FLRHW/Strobe_HMI/HTML/images/cat_pdf_drill_map_Strobe_HMI-PTH_drill_map.png

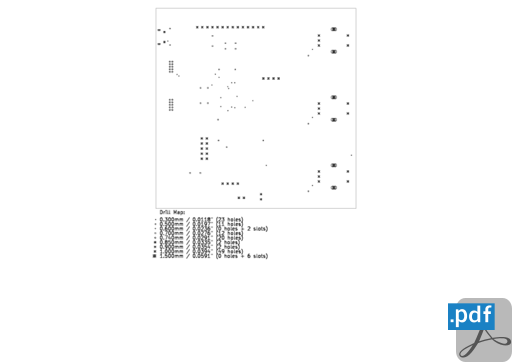
HTML/images/cat_pdf_drill_map_Strobe_HMI-PTH_drill_map.png
