FLRHW/Strobe_HMI/HTML/images/cat_png_3d_viewer_angled_bottom_Strobe_HMI-angled_bottom.png

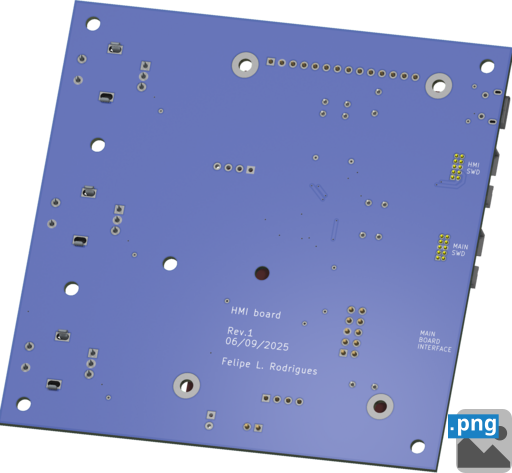
HTML/images/cat_png_3d_viewer_angled_bottom_Strobe_HMI-angled_bottom.png
