FLRHW/Strobe_HMI/HTML/images/cat_png_3d_viewer_angled_top_Strobe_HMI-angled_top.png

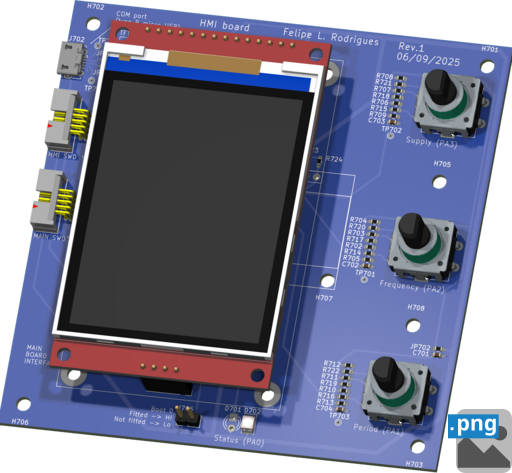
HTML/images/cat_png_3d_viewer_angled_top_Strobe_HMI-angled_top.png
