FLRHW/Strobe_HMI/HTML/images/cat_png_3d_viewer_top_Strobe_HMI-top.png

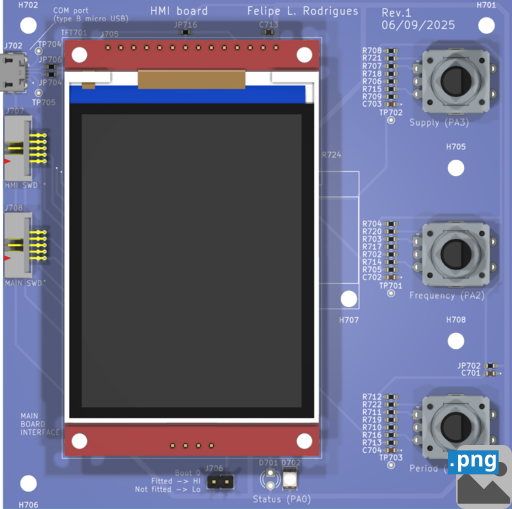
HTML/images/cat_png_3d_viewer_top_Strobe_HMI-top.png
