FLRHW/Strobe_HMI/Images/BOT.jpg

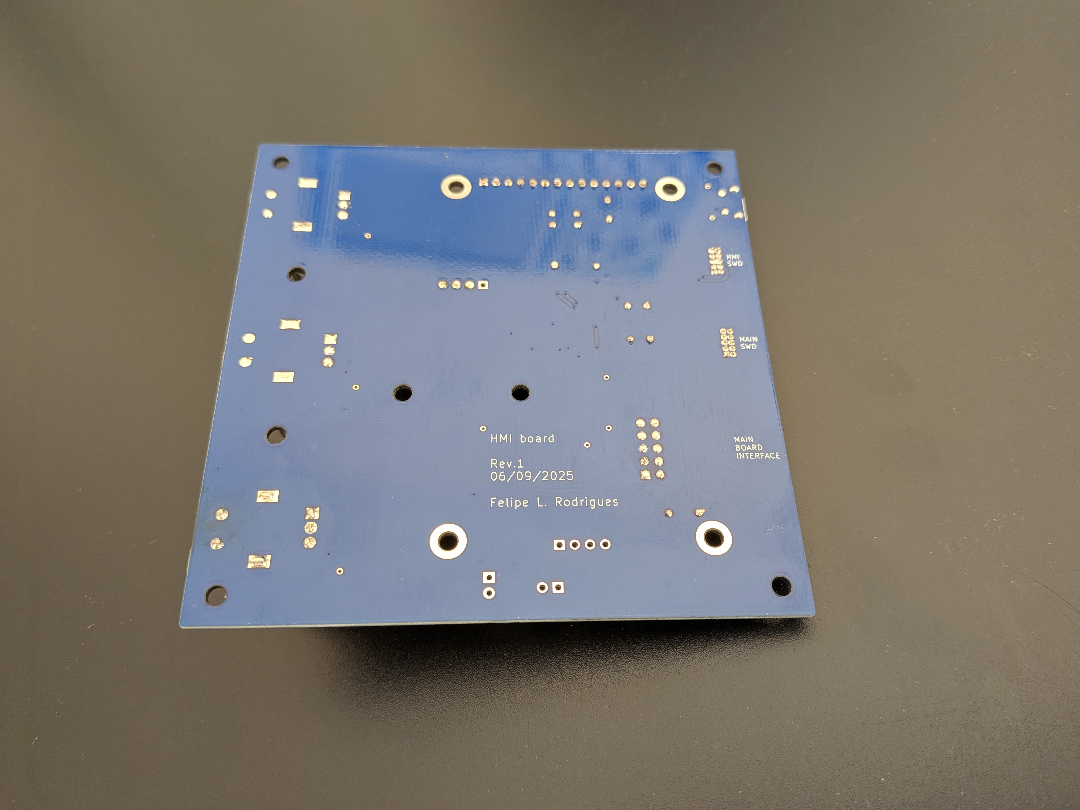
Images/BOT.jpg
